piot-jp-Team/ghf_sensorhousing/DSC_0026.jpg

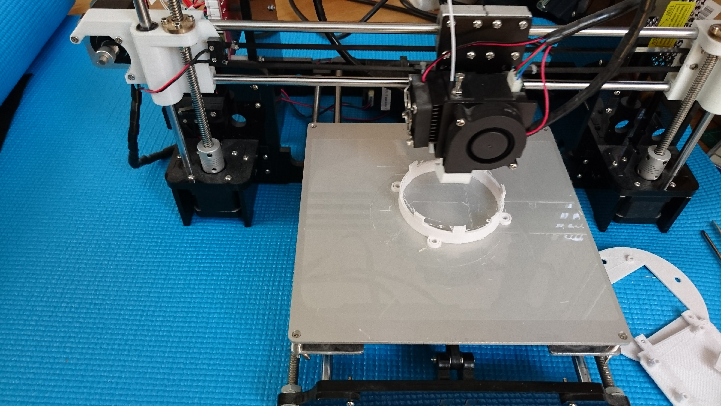
DSC_0026.jpg
