piot-jp-Team/ghf_sensorhousing/CAD/greenhouse_sens_bottomv2.stl

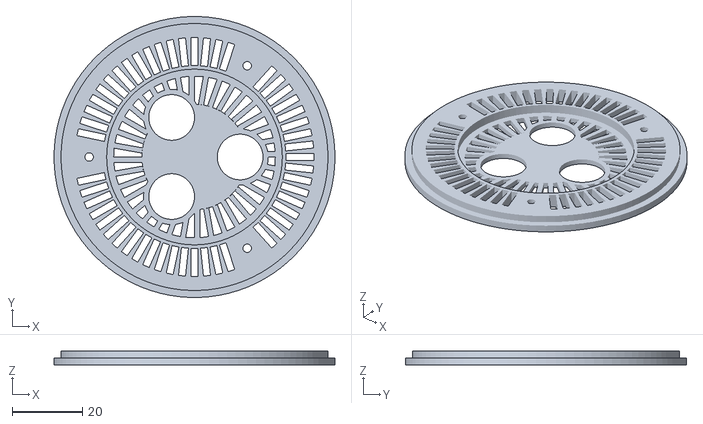
[picture p21: CAD file, 2018-11-20]
CAD/greenhouse_sens_bottomv2.stl
80.0 x 80.0 x 4.00
