piot-jp-Team/ghf_sensorhousing/CAD/greenhouse_sens_undershellv2.stl

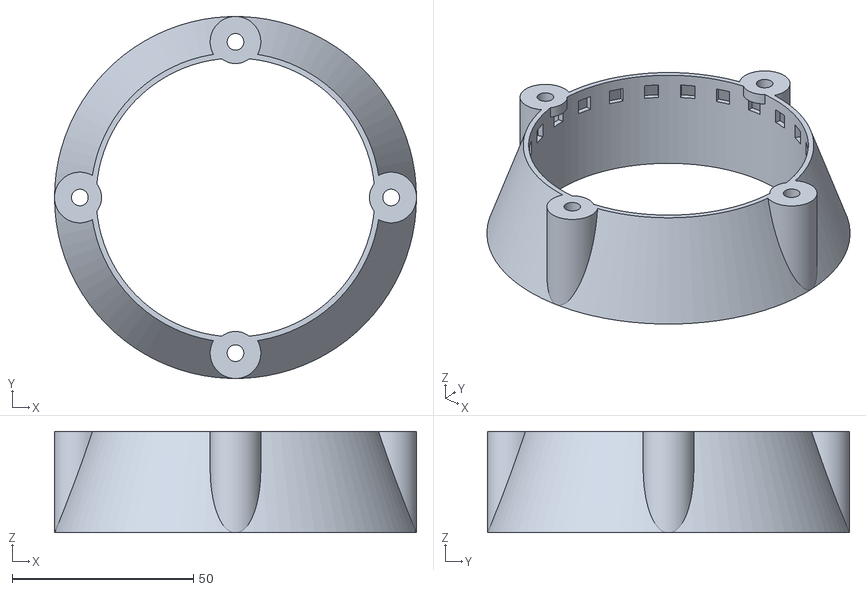
[picture p22: CAD file, 2018-11-19]
CAD/greenhouse_sens_undershellv2.stl
100.0 x 100.0 x 28.0
