piot-jp-Team/ghf_sensorhousing/CAD/greenhouse_sens_covertopv2.stl

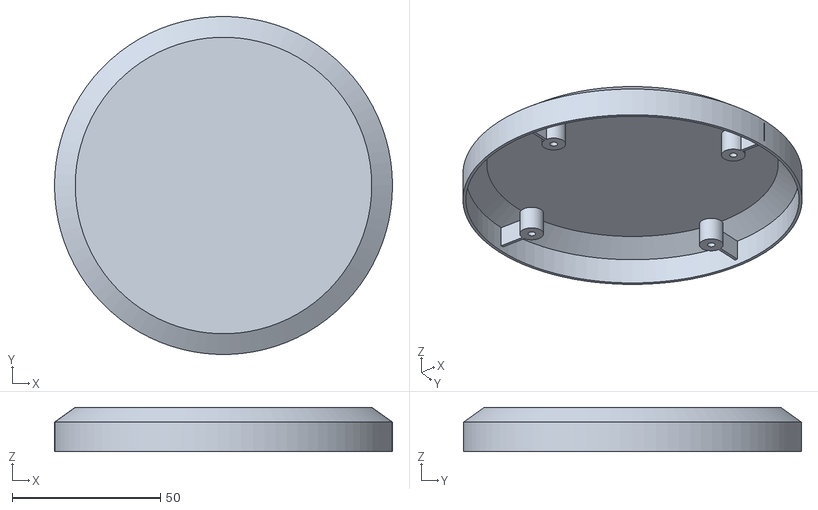
[picture p23: CAD file, 2018-11-16]
CAD/greenhouse_sens_covertopv2.stl
114.0 x 114.0 x 15.0
