piot-jp-Team/ghf_sensorhousing/CAD/undershell.step

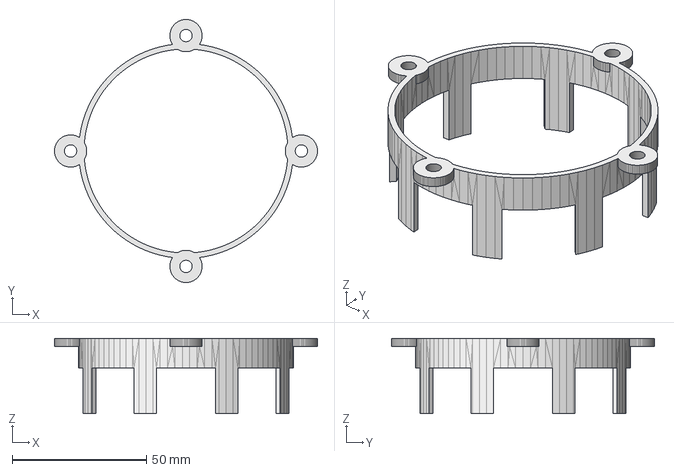
[picture p24: CAD file, 2018-11-06]
CAD/undershell.step
98.0 x 98.0 x 28.0 mm
