piot-jp-Team/ghf_sensorhousing/CAD/radiationsheildv3t.step

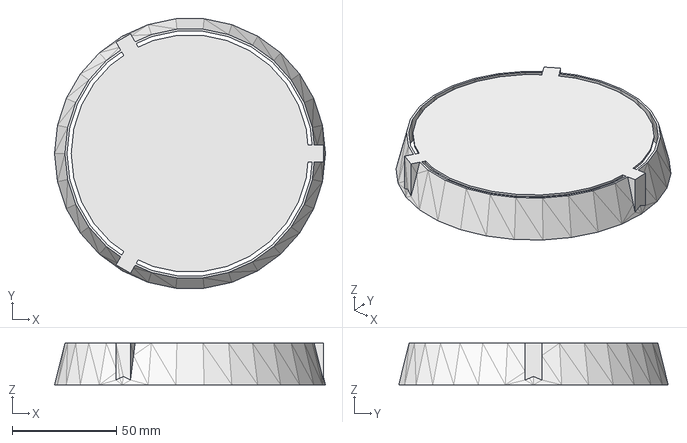
[picture p25: CAD file, 2018-11-06]
CAD/radiationsheildv3t.step
130.0 x 129.3 x 20.0 mm
