piot-jp-Team/ghf_sensorhousing/CAD/radiationsheildv3.step

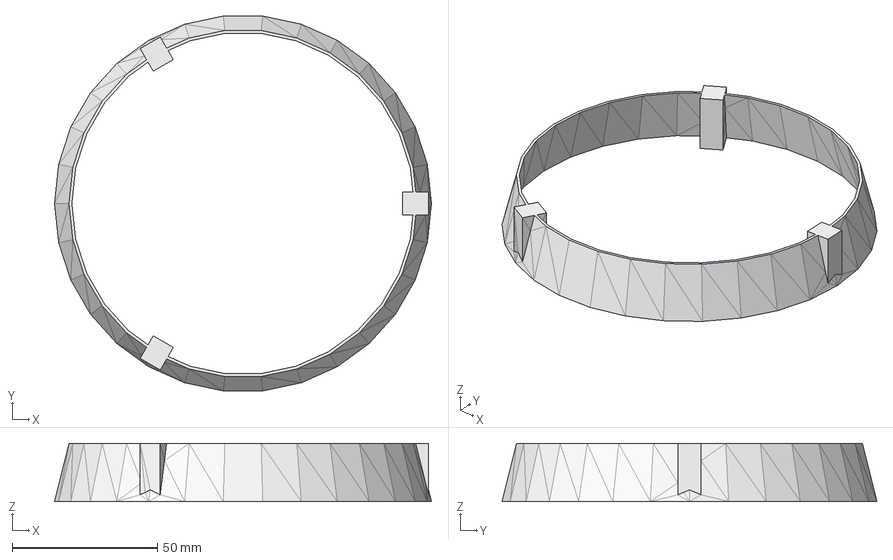
[picture p26: CAD file, 2018-11-06]
CAD/radiationsheildv3.step
130.0 x 129.3 x 20.0 mm
