piot-jp-Team/ghf_sensorhousing/CAD/bottom.step

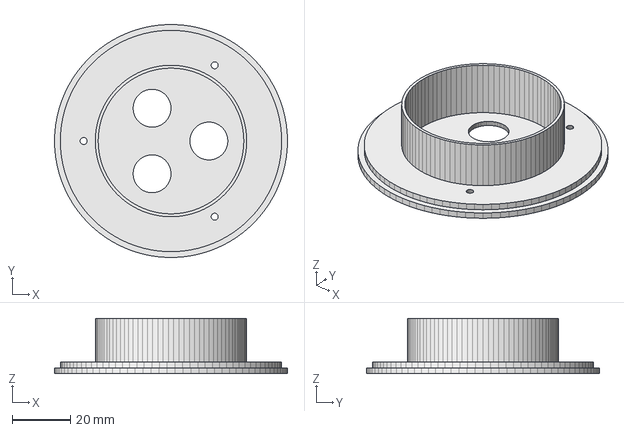
[picture p27: CAD file, 2018-11-06]
CAD/bottom.step
80.0 x 80.0 x 19.0 mm
