piot-jp-Team/ghf_sensorhousing/CAD/greenhouse_sens_v2_exp.stl

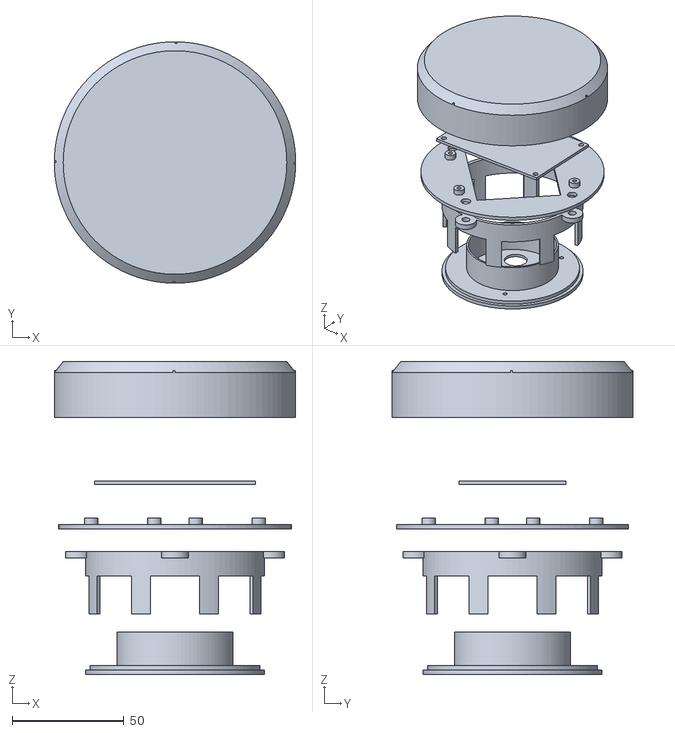
[picture p28: CAD file, 2018-10-11]
CAD/greenhouse_sens_v2_exp.stl
108.0 x 108.0 x 140.0
