piot-jp-Team/ghf_sensorhousing/CAD/greenhouse_sens_v2.stl

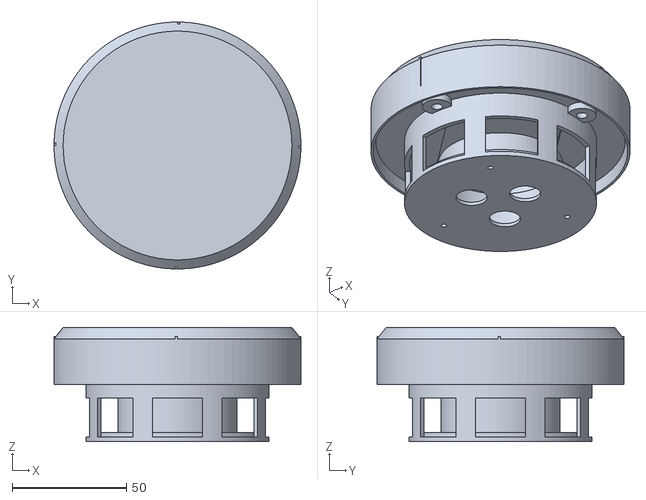
[picture p29: CAD file, 2018-10-11]
CAD/greenhouse_sens_v2.stl
108.0 x 108.0 x 50.0
