piot-jp-Team/ghf_sensorhousing/CAD/greenhouse_sens_kiban.stl

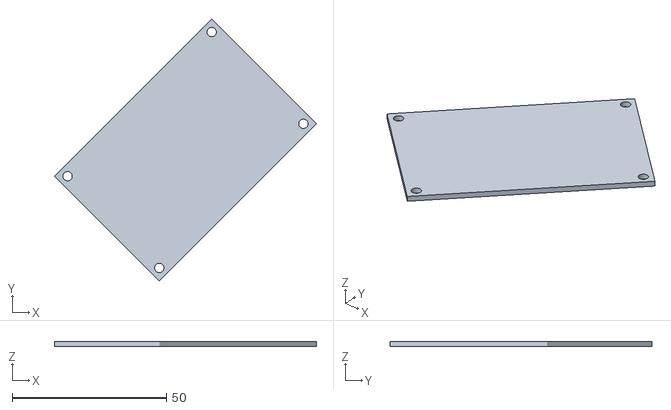
[picture p30: CAD file, 2018-10-11]
CAD/greenhouse_sens_kiban.stl
84.9 x 84.9 x 1.60
