piot-jp-Team/ghf_sensorhousing/CAD/greenhouse_sens_covertop.stl

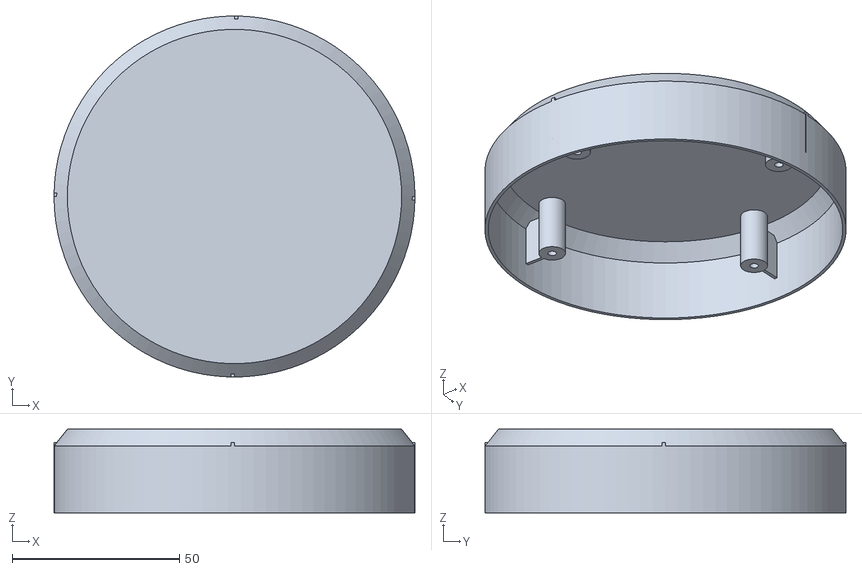
[picture p31: CAD file, 2018-10-11]
CAD/greenhouse_sens_covertop.stl
108.0 x 108.0 x 25.0
