piot-jp-Team/ghf_sensorhousing/CAD/ghf_caover_top_kinoko_die_sekkou_mold.stl

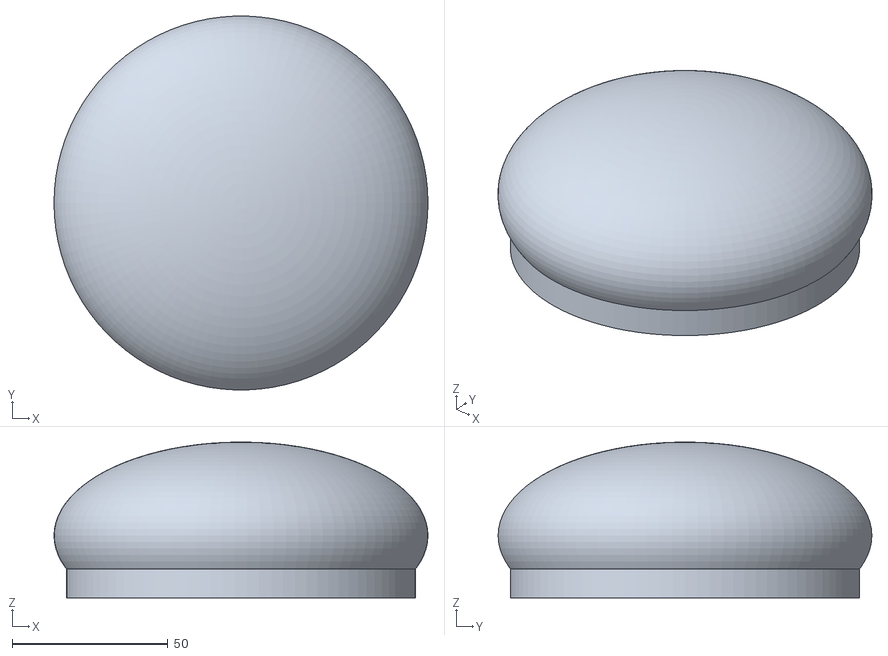
[picture p32: CAD file, 2018-06-02]
CAD/ghf_caover_top_kinoko_die_sekkou_mold.stl
120.0 x 119.9 x 50.0
