piot-jp-Team/ghf_sensorhousing/CAD/ghf_caover_top_kinoko_die.stl

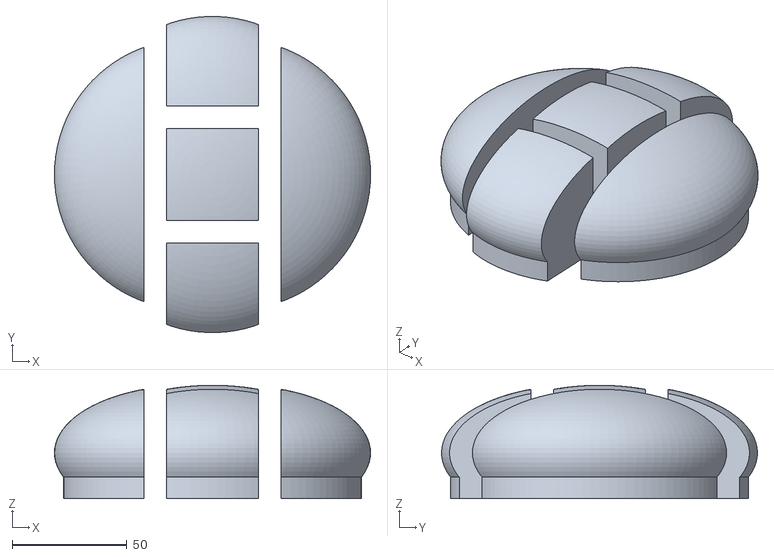
[picture p33: CAD file, 2018-05-21]
CAD/ghf_caover_top_kinoko_die.stl
138.0 x 137.9 x 49.5
