piot-jp-Team/ghf_sensorhousing/CAD/greenhouse_sensor_covertopkinoko.stl

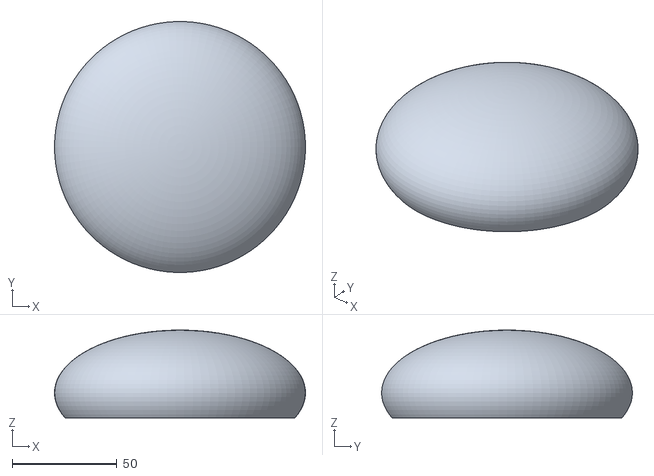
[picture p34: CAD file, 2018-05-17]
CAD/greenhouse_sensor_covertopkinoko.stl
120.0 x 119.9 x 42.0
