piot-jp-Team/ghf_sensorhousing/CAD/greenhouse_sens_kibanbasev2.scad

$fn = 90;

module kibanbase(){
union(){
    difference(){
    cylinder (r1 =49, r2 = 49, h= 6);
    cylinder (r1 =48, r2 = 48, h= 6);
    };

      difference(){
          cylinder (r1 =52, r2 = 52, h= 2);
//          translate ([-48/2,-60/2,0]){
//            cube ([48,60,2]);
//          }
          cylinder (r1 = 35, r2 = 35, h= 2);
          rotate ([0,0,45]) {translate ([43,0,0]) {
            cylinder (r1 = 2.8, r2 = 2.8, h= 2);}
          }    
          rotate ([0,0,135]) {translate ([43,0,0]) {
            cylinder (r1 = 2.8, r2 = 2.8, h= 2);}
          }         
          rotate ([0,0,225]) {translate ([43,0,0]) {
            cylinder (r1 = 2.8, r2 = 2.8, h= 2);}
          }    
          rotate ([0,0,-45]) {translate ([43,0,0]) {
            cylinder (r1 = 2.8, r2 = 2.8, h= 2);}
          }
        for ( i = [-6 : 6] )
        { 
            rotate( [0, 0, i * 360 / 60])
            translate ([40,0,0]){
            cube ([8,2,2]);
          }
        } 
        for ( i = [9 : 21] )
        { 
            rotate( [0, 0, i * 360 / 60])
            translate ([40,0,0]){
            cube ([8,2,2]);
          }
        }
        for ( i = [24 : 36] )
        { 
            rotate( [0, 0, i * 360 / 60])
            translate ([40,0,0]){
            cube ([8,2,2]);
          }
        }
        for ( i = [39 : 51] )
        { 
            rotate( [0, 0, i * 360 / 60])
            translate ([40,0,0]){
            cube ([8,2,2]);
          }
        }    
      }
      
        rotate ([0,0,0]) {
            translate ([33,21,0]){
                difference(){
                  cylinder (r1 = 3, r2 = 3, h= 5); 
                  cylinder (r1 = 1.2, r2 = 1.2, h= 5); 
                }
            }
            translate ([33,-21,0]){
                difference(){
                  cylinder (r1 = 3, r2 = 3, h= 5); 
                  cylinder (r1 = 1.2, r2 = 1.2, h= 5); 
                }
            }
            translate ([-33,21,0]){
                difference(){
                  cylinder (r1 = 3, r2 = 3, h= 5); 
                  cylinder (r1 = 1.2, r2 = 1.2, h= 5); 
                }
            }
            translate ([-33,-21,0]){
                difference(){
                  cylinder (r1 = 3, r2 = 3, h= 5); 
                  cylinder (r1 = 1.2, r2 = 1.2, h= 5); 
                }
            }
       }
    }
};

kibanbase();
