piot-jp-Team/ghf_sensorhousing/CAD/sakuraio_Holder/greenhouse_AntenaBracket.scad

include <arduino.scad>

//Arduino boards
//You can create a boxed out version of a variety of boards by calling the arduino() module
//The default board for all functions is the Uno

dueDimensions = boardDimensions( DUE );
unoDimensions = boardDimensions( UNO );

//Board mockups


/*
union() {
		//standoffs(LEONARDO, mountType=PIN);
       	standoffs(LEONARDO, mountType=TAPHOLE);
		boardShape(LEONARDO, offset = 3);
    
        translate([-13, 5, 0]) {
            difference(){
                cube([80,7,2]);
                translate([3.5, 3.5, 0]) {
                    cylinder (r1 = 2, r2 = 2, h= 2);
                }
                 translate([75.5, 3.5, 0]) {
                    cylinder (r1 = 2, r2 = 2, h= 2);
                }
            }
        }
        
         translate([-13, 55, 0]) {
            difference(){
                cube([80,7,2]);
                translate([3.5, 3.5, 0]) {
                    cylinder (r1 = 2, r2 = 2, h= 2);
                }
                 translate([75.5, 3.5, 0]) {
                    cylinder (r1 = 2, r2 = 2, h= 2);
                }
            }
        }


        
	}
*/

    rotate([90, 0, 0]){
        union(){
            translate([-35, 0, 0]) {
                difference(){
                    cube([70,12,3]);
                    translate([20, 5, 0])
                        cylinder (r1 = 2, r2 = 2, h= 6);
                    translate([20+10.5, 5, 0])
                        cylinder (r1 = 2, r2 = 2, h= 6);
                    translate([3*20+20-30, 5, 0])
                        cylinder (r1 = 2, r2 = 2, h= 6);
                     translate([3*20+20-30-10.5, 5, 0])
                        cylinder (r1 = 2, r2 = 2, h= 6);
                    translate([34.5, 0, 1])cube([1,15,4]);
                }
            }
            translate([-35, 0, 0]) {
                difference(){
                    cube([14,5,50]);
                    translate([7, 0, 41]) {
                        rotate([-90, 0, 0]){
                            cylinder (r1 = 4.1, r2 = 4.1, h= 6);
                        }
                    }
                    translate([7, 0, 41]) {
                        rotate([-90, 0, 0]){
                            translate([0, 0, 1.5])cylinder (r1 = 6.1, r2 = 6.1, h= 4.5);
                        }
                    }
                }
            }
            translate([21, 0, 0]) {
                difference(){
                    cube([14,5,50]);
                    translate([7, 0, 41]) {
                        rotate([-90, 0, 0]){
                            cylinder (r1 = 4.1, r2 = 4.1, h= 6);
                        }
                    }
                    translate([7, 0, 41]) {
                        rotate([-90, 0, 0]){
                            translate([0, 0, 1.5])cylinder (r1 = 6.1, r2 = 6.1, h= 4.5);
                        }
                    }
                }
            }
        }
    }
    
/*
translate([0, 0, 10]) {
	arduino();
}
*/
